Xinyuan-LilyGO/T-Embed-CC1101/hardware/SI446X/T-SI4463 V0.1-PIN.pdf

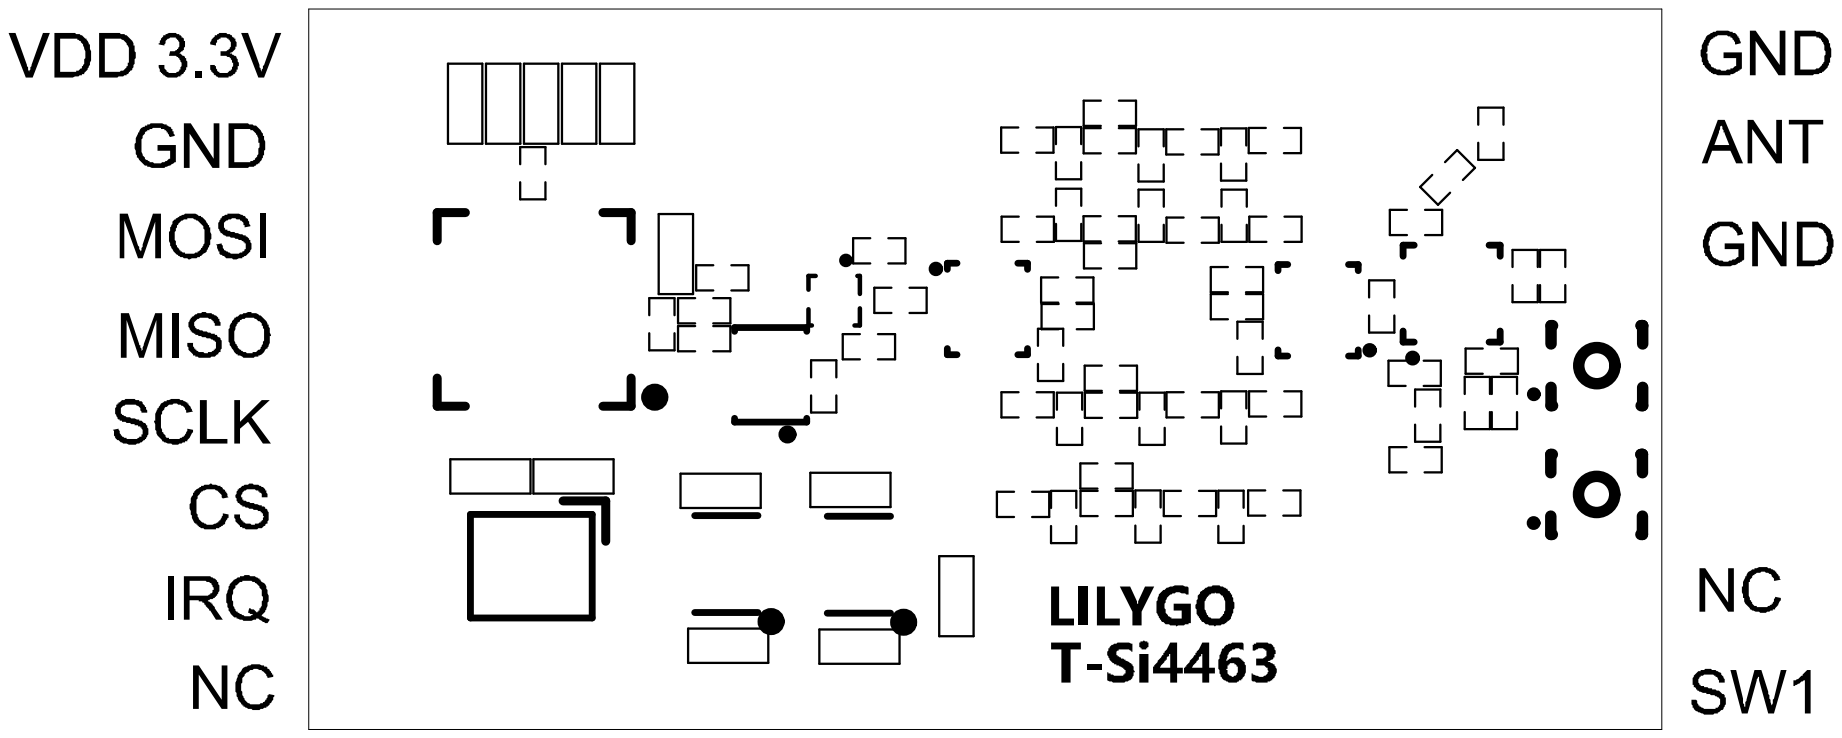
[picture p25: page 1]
