Xinyuan-LilyGO/T-Embed-CC1101/examples/factory_test/factory_test.ino

#include "utilities.h"
#define XPOWERS_CHIP_BQ25896
#include <XPowersLib.h>
#include "ui.h"
#include "TFT_eSPI.h"
#include "Audio.h"
#include <IRremoteESP8266.h>
#include <IRsend.h>
#include <IRrecv.h>
#include <IRutils.h>

const uint16_t kIrLed = 2;  // ESP8266 GPIO pin to use. Recommended: 4 (D2).
const uint16_t kRecvPin = 1;
IRsend irsend(kIrLed);  // Set the GPIO to be used to sending the message.
IRrecv irrecv(kRecvPin);
decode_results results;

uint64_t IR_recv_value = 0x10000000UL;
char IR_recv_protocol[20] = "WAIT";
uint16_t IR_recv_bits = 0;
bool IR_recv_repeat = false;
uint32_t IR_recv_count = 0;
uint32_t IR_recv_last_ms = 0;

/*********************************************************************************
 *                               DEFINE
 *********************************************************************************/
#define FORMAT_SPIFFS_IF_FAILED true

#define NFC_PRIORITY     (configMAX_PRIORITIES - 1)
#define LORA_PRIORITY    (configMAX_PRIORITIES - 2)
#define WS2812_PRIORITY  (configMAX_PRIORITIES - 3)
#define BATTERY_PRIORITY (configMAX_PRIORITIES - 4)
#define NRF24_PRIORITY   (tskIDLE_PRIORITY + 2)

/*********************************************************************************
 *                              EXTERN
 *********************************************************************************/
extern uint8_t display_rotation;
extern uint8_t setting_theme;
/*********************************************************************************
 *                              TYPEDEFS
 *********************************************************************************/

Audio audio(false, 3, I2S_NUM_1);
XPowersPPM PPM;
BQ27220 bq27220;
uint32_t cycleInterval;
SemaphoreHandle_t radioLock;

TaskHandle_t nfc_handle;
TaskHandle_t lora_handle;
TaskHandle_t ws2812_handle;
TaskHandle_t battery_handle;
TaskHandle_t nrf24_handle;

// wifi
// char wifi_ssid[WIFI_SSID_MAX_LEN] = "xinyuandianzi";
// char wifi_password[WIFI_PSWD_MAX_LEN] = "AA15994823428";
char wifi_ssid[WIFI_SSID_MAX_LEN] = {0};
char wifi_password[WIFI_PSWD_MAX_LEN] = {0};
const char *ntpServer1 = "pool.ntp.org";
const char* ntpServer2 = "time.nist.gov";
bool wifi_is_connect = false;
bool wifi_eeprom_upd = false;
static struct tm timeinfo;
static uint32_t last_tick;

static constexpr uint16_t PPM_INPUT_LIMIT_MA = 1000;
static constexpr uint16_t PPM_CHARGE_TARGET_MV = 4208;
static constexpr uint16_t PPM_PRECHARGE_MA = 128;
static constexpr uint16_t PPM_TERMINATION_MA = 128;
static constexpr uint16_t PPM_FAST_CHARGE_MA = 512;
static constexpr uint16_t PPM_SYS_POWERDOWN_MV = 3300;
static constexpr uint32_t PPM_RECOVERY_RETRY_INTERVAL_MS = 1500;
static constexpr int16_t PPM_RECOVERY_DISCHARGE_CURRENT_MA = -50;
static constexpr uint32_t MIC_SAMPLE_PERIOD_MS = 5;
static constexpr TickType_t MIC_SAMPLE_TIMEOUT_TICKS = 0;
static constexpr uint32_t BOARD_USER_KEY_DEBOUNCE_MS = 30;

static bool ppm_recovery_enabled = true;
static bool ppm_recovery_usb_was_present = false;
static uint32_t ppm_recovery_last_ms = 0;

// eeprom
uint8_t eeprom_ssid[WIFI_SSID_MAX_LEN];
uint8_t eeprom_pswd[WIFI_PSWD_MAX_LEN];

// mic
int16_t i2s_readraw_buff[SAMPLE_SIZE] = {0};
size_t bytes_read = 0;
int i2s_mic_cnt = 0;

/*********************************************************************************
 *                              FUNCTION
 *********************************************************************************/

static void board_spi_init_cs_pin(uint8_t pin)
{
    pinMode(pin, OUTPUT);
    digitalWrite(pin, HIGH);
}

void board_spi_deselect_all(void)
{
    digitalWrite(DISPLAY_CS, HIGH);
    digitalWrite(BOARD_SD_CS, HIGH);
    digitalWrite(BOARD_LORA_CS, HIGH);
    digitalWrite(BOARD_NRF24_CS, HIGH);
}

void board_spi_prepare_display(void)
{
    board_spi_deselect_all();
}

void board_spi_prepare_lora(void)
{
    board_spi_deselect_all();
}

void board_spi_prepare_nrf24(void)
{
    board_spi_deselect_all();
}

void board_spi_prepare_sd(void)
{
    board_spi_deselect_all();
}

void board_spi_init_shared_bus(void)
{
    board_spi_init_cs_pin(DISPLAY_CS);
    board_spi_init_cs_pin(BOARD_SD_CS);
    board_spi_init_cs_pin(BOARD_LORA_CS);
    board_spi_init_cs_pin(BOARD_NRF24_CS);

    pinMode(BOARD_NRF24_CE, OUTPUT);
    digitalWrite(BOARD_NRF24_CE, LOW);

    board_spi_deselect_all();
    SPI.begin(BOARD_SPI_SCK, BOARD_SPI_MISO, BOARD_SPI_MOSI);
}

void eeprom_default_val(void)
{
    char wifi_ssid[WIFI_SSID_MAX_LEN] = "xinyuandianzi";
    char wifi_password[WIFI_PSWD_MAX_LEN] = "AA15994823428";

    EEPROM.write(0, EEPROM_UPDATA_FLAG_NUM);
    for(int i = WIFI_SSID_EEPROM_ADDR; i < WIFI_SSID_EEPROM_ADDR + WIFI_SSID_MAX_LEN; i++) {
        int k = i - WIFI_SSID_EEPROM_ADDR;
        if(k < WIFI_SSID_MAX_LEN) {
            EEPROM.write(i, wifi_ssid[k]);
        } else {
            EEPROM.write(i, 0x00);
        }
    }
    for(int i = WIFI_PSWD_EEPROM_ADDR; i < WIFI_PSWD_EEPROM_ADDR + WIFI_PSWD_MAX_LEN; i++) {
        int k = i - WIFI_PSWD_EEPROM_ADDR;
        if(k < WIFI_PSWD_MAX_LEN) {
            EEPROM.write(i, wifi_password[k]);
        } else {
            EEPROM.write(i, 0x00);
        }
    }
    EEPROM.commit();
    wifi_eeprom_upd = true;
}

void eeprom_wr(int addr, uint8_t val)
{
    if(wifi_eeprom_upd == false) {
        eeprom_default_val();
    }
    EEPROM.write(addr, val);
    EEPROM.commit();
    Serial.printf("eeprom_wr %d:%d\n", addr, val);
}

void eeprom_wr_wifi(const char *ssid, uint16_t ssid_len, const char *pwsd, uint16_t pwsd_len)
{
    Serial.printf("eeprom_wr_wifi \n%s:%d\n%s:%d\n", ssid, ssid_len, pwsd, pwsd_len);
    if(ssid_len > WIFI_SSID_MAX_LEN) 
        ssid_len = WIFI_SSID_MAX_LEN;
    if(pwsd_len > WIFI_PSWD_MAX_LEN)
        pwsd_len = WIFI_PSWD_MAX_LEN;

    if(wifi_eeprom_upd == false) {
        EEPROM.write(0, EEPROM_UPDATA_FLAG_NUM);
        wifi_eeprom_upd = true;
    }

    for(int i = WIFI_SSID_EEPROM_ADDR; i < WIFI_SSID_EEPROM_ADDR + WIFI_SSID_MAX_LEN; i++) {
        int k = i - WIFI_SSID_EEPROM_ADDR;
        if(k < ssid_len) {
            EEPROM.write(i, ssid[k]);
        } else {
            EEPROM.write(i, 0x00);
        }
    }
    for(int i = WIFI_PSWD_EEPROM_ADDR; i < WIFI_PSWD_EEPROM_ADDR + WIFI_PSWD_MAX_LEN; i++) {
        int k = i - WIFI_PSWD_EEPROM_ADDR;
        if(k < pwsd_len) {
            EEPROM.write(i, pwsd[k]);
        } else {
            EEPROM.write(i, 0x00);
        }
    }
    EEPROM.commit();
}

void eeprom_init()
{
    if (!EEPROM.begin(EEPROM_SIZE_MAX)) {
        Serial.println("failed to initialise EEPROM"); delay(1000000);
    }
    uint8_t frist_flag = EEPROM.read(0);
    if(frist_flag == EEPROM_UPDATA_FLAG_NUM) {
        for(int i = WIFI_SSID_EEPROM_ADDR; i < WIFI_SSID_EEPROM_ADDR + WIFI_SSID_MAX_LEN; i++) {
            wifi_ssid[i - WIFI_SSID_EEPROM_ADDR] = EEPROM.read(i);
        }
        for(int i = WIFI_PSWD_EEPROM_ADDR; i < WIFI_PSWD_EEPROM_ADDR + WIFI_PSWD_MAX_LEN; i++) {
            wifi_password[i - WIFI_PSWD_EEPROM_ADDR] = EEPROM.read(i);
        }

        wifi_eeprom_upd = true;
        

        uint8_t theme = EEPROM.read(UI_THEME_EEPROM_ADDR);
        uint8_t rotation = EEPROM.read(UI_ROTATION_EEPROM_ADDR);

        setting_theme = (theme == 255 ? 0 : theme);
        display_rotation = (rotation == 1 ? 1 : 3);

        Serial.println("*************** eeprom ****************");
        Serial.printf("eeprom flag: %d\n", frist_flag);
        Serial.printf("eeprom SSID: %s\n", wifi_ssid);
        Serial.printf("eeprom PWSD: %s\n", wifi_password);
        Serial.printf("eeprom theme: %d\n", theme);
        Serial.printf("eeprom rotation: %d\n", rotation);
        Serial.println("***************************************");
    }
}

void multi_thread_create(void)
{
    xTaskCreate(nfc_task, "nfc_task", 1024 * 3, NULL, NFC_PRIORITY, &nfc_handle);
    xTaskCreate(lora_task, "lora_task", 1024 * 2, NULL, LORA_PRIORITY, &lora_handle);
    xTaskCreate(ws2812_task, "ws2812_task", 1024 * 2, NULL, WS2812_PRIORITY, &ws2812_handle);
    xTaskCreate(nrf24_task, "nrf24_task", 1024 * 10, NULL, NRF24_PRIORITY, &nrf24_handle);
}

void wifi_init(void)
{
    Serial.printf("SSID len: %d\n", strlen(wifi_ssid));
    Serial.printf("PWSD len: %d\n", strlen(wifi_password));
    if(strlen(wifi_ssid) == 0 || strlen(wifi_password) == 0) {
        return;
    }

    WiFi.begin(wifi_ssid, wifi_password);
    wl_status_t wifi_state = WiFi.status();
    last_tick = millis();
    while (wifi_state != WL_CONNECTED){
        delay(500);
        Serial.print(".");
        wifi_state = WiFi.status();
        if(wifi_state == WL_CONNECTED){
            wifi_is_connect = true;
            Serial.println("WiFi connected!");
            configTime(8 * 3600, 0, ntpServer1, ntpServer2);
            break;
        }
        if (millis() - last_tick > 5000) {
            Serial.println("WiFi connected falied!");
            last_tick = millis();
            break;
        }
    }
}

static void msg_send_event(lv_timer_t *t)
{
    if(wifi_is_connect == true){
        if (!getLocalTime(&timeinfo)){
            Serial.println("Failed to obtain time");
            return;
        }
        // Serial.println(&timeinfo, "%F %T %A"); // 格式化输出
        timeinfo.tm_hour = timeinfo.tm_hour % 12;
        lv_msg_send(MSG_CLOCK_HOUR, &timeinfo.tm_hour);
        lv_msg_send(MSG_CLOCK_MINUTE, &timeinfo.tm_min);
        lv_msg_send(MSG_CLOCK_SECOND, &timeinfo.tm_sec);
    }
}

static void msg_subsribe_event(void * s, lv_msg_t * msg)
{
    LV_UNUSED(s);

    switch (msg->id)
    {
        case MSG_UI_ROTATION_ST:{ 
            
        }break;
        case MSG_UI_THEME_MODE:{
            
        }break;
    
        default:
            break;
    }
}

void listDir(fs::FS &fs, const char * dirname, uint8_t levels){
    Serial.printf("Listing spiffs directory: %s\n", dirname);

    File root = fs.open(dirname);
    if(!root){
        Serial.println("- failed to open directory");
        return;
    }
    if(!root.isDirectory()){
        Serial.println(" - not a directory");
        return;
    }

    File file = root.openNextFile();
    while(file){
        if(file.isDirectory()){
            Serial.print("  DIR : ");
            Serial.println(file.name());
            if(levels){
                listDir(fs, file.path(), levels -1);
            }
        } else {
            Serial.print("  FILE: ");
            Serial.print(file.name());
            Serial.print("\tSIZE: ");
            Serial.println(file.size());
        }
        file = root.openNextFile();
    }
}

extern int music_idx;
extern char *music_list[20];

void scr8_read_music_from_SD(void)
{
    board_spi_prepare_sd();

    File root = SD.open("/music");
    if(!root){
        Serial.println("Failed to open directory");
        return;
    }

    int i = 0;
    File file = root.openNextFile();
    while(file) {
        if(!file.isDirectory()) {
            
            char *file_name = (char *)file.name();
            uint16_t file_name_len = strlen(file_name);
            char *buf = (char *)ps_malloc(file_name_len + 1);
            strcpy(buf, file_name);
            music_list[i] = buf;
            i++;

            Serial.println(music_list[i-1]);
        }
        file = root.openNextFile();
    }
}

static bool ppm_usb_present(void)
{
    return PPM.isVbusIn() || (PPM.getVbusVoltage() >= 4000);
}

static void ppm_configure_charge_path(bool reset_registers)
{
    if (reset_registers) {
        PPM.resetDefault();
        delay(20);
    }

    PPM.disableWatchdog();
    PPM.exitHizMode();
    PPM.disableOTG();
    PPM.enableBatterPowerPath();
    PPM.disableCurrentLimitPin();
    PPM.enableAutomaticInputDetection();
    PPM.enableInputDetection();
    PPM.setInputCurrentLimit(PPM_INPUT_LIMIT_MA);
    PPM.setChargeTargetVoltage(PPM_CHARGE_TARGET_MV);
    PPM.setPrechargeCurr(PPM_PRECHARGE_MA);
    PPM.setTerminationCurr(PPM_TERMINATION_MA);
    PPM.setChargerConstantCurr(PPM_FAST_CHARGE_MA);
    PPM.enableMeasure();
    PPM.enableChargingTermination();
    PPM.setSysPowerDownVoltage(PPM_SYS_POWERDOWN_MV);
    PPM.enableCharge();
    PPM.getFaultStatus();
}

static bool ppm_needs_charge_recovery(void)
{
    if (!ppm_usb_present()) {
        return false;
    }

    uint16_t battery_mv = PPM.getBattVoltage();
    uint16_t target_mv = PPM.getChargeTargetVoltage();
    bool battery_needs_charge = (battery_mv == 0) || (target_mv == 0) || (battery_mv + 96 < target_mv);
    bool charge_path_invalid = PPM.isHizMode() || PPM.isEnableOTG() || !PPM.isEnableCharge();
    bool charge_state_missing = PPM.chargeStatus() == XPowersPPM::CHARGE_STATE_NO_CHARGE;
    bool power_not_good = !PPM.isPowerGood();
    bool battery_still_discharging = bq27220.getAverageCurrent() <= PPM_RECOVERY_DISCHARGE_CURRENT_MA;

    return charge_path_invalid || (battery_needs_charge && (charge_state_missing || power_not_good || battery_still_discharging));
}

static void ppm_service_charge_recovery(void)
{
    if (!ppm_recovery_enabled) {
        return;
    }

    bool usb_present = ppm_usb_present();
    if (usb_present && !ppm_recovery_usb_was_present) {
        Serial.println("VBUS inserted, restoring BQ25896 charge path.");
        ppm_configure_charge_path(true);
        ppm_recovery_last_ms = millis();
    } else if (usb_present && ppm_needs_charge_recovery()) {
        uint32_t now = millis();
        if ((ppm_recovery_last_ms == 0) || (now - ppm_recovery_last_ms >= PPM_RECOVERY_RETRY_INTERVAL_MS)) {
            Serial.printf("BQ25896 recovery: bus=%d chg=%d vbus=%umV vbat=%umV avg=%dmA hiz=%d otg=%d enchg=%d pg=%d\n",
                          (int)PPM.getBusStatus(),
                          (int)PPM.chargeStatus(),
                          PPM.getVbusVoltage(),
                          PPM.getBattVoltage(),
                          bq27220.getAverageCurrent(),
                          (int)PPM.isHizMode(),
                          (int)PPM.isEnableOTG(),
                          (int)PPM.isEnableCharge(),
                          (int)PPM.isPowerGood());
            ppm_configure_charge_path(true);
            ppm_recovery_last_ms = now;
        }
    }

    if (!usb_present) {
        ppm_recovery_last_ms = 0;
    }
    ppm_recovery_usb_was_present = usb_present;
}

void ppm_set_recovery_enabled(bool enabled)
{
    ppm_recovery_enabled = enabled;
    if (enabled) {
        ppm_recovery_usb_was_present = false;
        ppm_recovery_last_ms = 0;
    }
}

static bool board_user_key_pressed(void)
{
    static bool last_raw_state = HIGH;
    static bool stable_state = HIGH;
    static uint32_t last_change_ms = 0;

    bool raw_state = digitalRead(BOARD_USER_KEY);
    uint32_t now = millis();

    if (raw_state != last_raw_state) {
        last_raw_state = raw_state;
        last_change_ms = now;
    }

    if ((now - last_change_ms) >= BOARD_USER_KEY_DEBOUNCE_MS && stable_state != raw_state) {
        stable_state = raw_state;
        if (stable_state == LOW) {
            return true;
        }
    }

    return false;
}

void setup(void)
{
    bool pmu_ret = false;
    bool nfc_ret = false;
    bool lora_ret = false;

    // LCD, CC1101, SD and nRF24 share the same SPI lines, keep every device
    // deselected before any library touches the bus.
    board_spi_init_shared_bus();

    // Init system
    pinMode(DISPLAY_BL, OUTPUT);
    digitalWrite(DISPLAY_BL, LOW);

    pinMode(BOARD_PWR_EN, OUTPUT);
    digitalWrite(BOARD_PWR_EN, HIGH);  // Power on CC1101 and LED

    pinMode(BOARD_PN532_RF_REST, OUTPUT);
    digitalWrite(BOARD_PN532_RF_REST, HIGH); 

    pinMode(ENCODER_KEY, INPUT);
    pinMode(BOARD_USER_KEY, INPUT);

    pinMode(BOARD_PN532_IRQ, OPEN_DRAIN);

    Serial.begin(115200);
    Serial.print("setup() running core ID: ");
    Serial.println(xPortGetCoreID());

    irsend.begin();
    irrecv.enableIRIn(); 

    radioLock = xSemaphoreCreateBinary();
    assert(radioLock);
    xSemaphoreGive(radioLock);

    init_microphone();

    // iic scan
    byte error, address;
    int nDevices = 0;
    Serial.println("Scanning for I2C devices ...");
    Wire.begin(BOARD_I2C_SDA, BOARD_I2C_SCL);
    for(address = 0x01; address < 0x7F; address++){
        Wire.beginTransmission(address);
        // 0: success.
        // 1: data too long to fit in transmit buffer.
        // 2: received NACK on transmit of address.
        // 3: received NACK on transmit of data.
        // 4: other error.
        // 5: timeout
        error = Wire.endTransmission();
        if(error == 0){ // 0: success.
            nDevices++;
            if(address == BOARD_I2C_ADDR_1) {
                nfc_ret = true;
                log_i("I2C device found PN532 at address 0x%x\n", address);
            } else if(address == BOARD_I2C_ADDR_2) {
                pmu_ret = true;
                log_i("I2C device found at BQ27220 address 0x%x\n", address);
            } else if(address == BOARD_I2C_ADDR_3) {
                lora_ret = true;
                log_i("I2C device found at BQ25896 address 0x%x\n", address);
            }
        }
    }
    if (nDevices == 0){
        Serial.println("No I2C devices found");
    }

    if(!SPIFFS.begin(FORMAT_SPIFFS_IF_FAILED)){
        Serial.println("SPIFFS Mount Failed");
        return;
    }

    Serial.println("*************** SPIFFS ****************");
    listDir(SPIFFS, "/", 0);
    Serial.println("**************************************");

    eeprom_init();

    // wifi_init();
    configTime(8 * 3600, 0, ntpServer1, ntpServer2);

    pmu_ret = PPM.init(Wire, BOARD_I2C_SDA, BOARD_I2C_SCL, BQ25896_SLAVE_ADDRESS);
    if(pmu_ret) {
        ppm_configure_charge_path(true);

        Serial.printf("BQ25896 input limit: %d mA\n", PPM.getInputCurrentLimit());
        Serial.printf("BQ25896 fast charge current: %d mA\n", PPM.getChargerConstantCurr());
        Serial.printf("BQ25896 termination current: %d mA\n", PPM.getTerminationCurr());
        Serial.printf("BQ25896 sys power down voltage: %d mV\n", PPM.getSysPowerDownVoltage());
        // Turn off charging function
        // If USB is used as the only power input, it is best to turn off the charging function,
        // otherwise the VSYS power supply will have a sawtooth wave, affecting the discharge output capability.
        // PPM.disableCharge();


        // The OTG function needs to enable OTG, and set the OTG control pin to HIGH
        // After OTG is enabled, if an external power supply is plugged in, OTG will be turned off

        // PPM.enableOTG();
        // PPM.disableOTG();
        // pinMode(OTG_ENABLE_PIN, OUTPUT);
        // digitalWrite(OTG_ENABLE_PIN, HIGH);
    }

    bq27220.init();
   
    lora_init(); 

    if(nfc_ret)
        nfc_init();

    ws2812_init();

    // infared_init();

    nrf24_init();

    audio.setPinout(BOARD_VOICE_BCLK, BOARD_VOICE_LRCLK, BOARD_VOICE_DIN);
    audio.setVolume(21); // 0...21
    audio.connecttoFS(SPIFFS, "/001.mp3");

    // audio.connecttoFS(SD, "/music/My Anata.mp3");

    Serial.println("setup: ble_uart_init");
    ble_uart_init();
    delay(1);

    // init UI and display
    Serial.println("setup: ui_entry");
    ui_entry();
    delay(1);
    lv_timer_create(msg_send_event, 5000, NULL);
    // lvgl msg
    lv_msg_subsribe(MSG_UI_ROTATION_ST, msg_subsribe_event, NULL);
    lv_msg_subsribe(MSG_UI_THEME_MODE, msg_subsribe_event, NULL);

    // Force the first frame out before enabling the backlight so we don't
    // spend the SD probe window showing a lit-but-empty panel.
    Serial.println("setup: first lv_timer_handler");
    lv_timer_handler();
    digitalWrite(DISPLAY_BL, HIGH);
    delay(1);

    Serial.println("setup: sd_init");
    sd_init();
    Serial.println("setup: scr8_read_music_from_SD");
    scr8_read_music_from_SD();
    delay(1);

    Serial.println("setup: multi_thread_create");
    multi_thread_create();

    // for(int i = 0; i < WS2812_NUM_LEDS*10; i++) {
    //     ws2812_pos_demo(i);
    //     delay(15);
    // }
    // ws2812_set_color(CRGB::Black);

    
}

int file_cnt = 0;
extern bool music_is_running;

void loop(void)
{
    static uint32_t last_mic_sample_ms = 0;

    audio.loop();

    lv_timer_handler();
    ble_uart_service();

    ppm_service_charge_recovery();

    if (board_user_key_pressed()) {
        Serial.println("BOARD_USER_KEY pressed");
        prompt_info("BOARD_USER_KEY pressed", 800);
    }

    if(music_is_running == false) {
        if (irrecv.decode(&results)) {
            // print() & println() can't handle printing long longs. (uint64_t)
            serialPrintUint64(results.value, HEX);
            IR_recv_value = results.value;
            IR_recv_bits = results.bits;
            IR_recv_repeat = results.repeat;
            IR_recv_count++;
            IR_recv_last_ms = millis();

            String protocol = typeToString(results.decode_type, results.repeat);
            protocol.toUpperCase();
            strncpy(IR_recv_protocol, protocol.c_str(), sizeof(IR_recv_protocol) - 1);
            IR_recv_protocol[sizeof(IR_recv_protocol) - 1] = '\0';
            Serial.println("");
            irrecv.resume();  // Receive the next value
        }

        uint32_t now = millis();
        if ((now - last_mic_sample_ms) >= MIC_SAMPLE_PERIOD_MS) {
            last_mic_sample_ms = now;
            if (i2s_read((i2s_port_t)EXAMPLE_I2S_CH,
                         (char *)i2s_readraw_buff,
                         sizeof(i2s_readraw_buff),
                         &bytes_read,
                         MIC_SAMPLE_TIMEOUT_TICKS) == ESP_OK) {
                size_t sample_count = bytes_read / sizeof(i2s_readraw_buff[0]);
                if (sample_count > SAMPLE_SIZE) {
                    sample_count = SAMPLE_SIZE;
                }

                for(size_t i = 0; i < sample_count; i++) {
                    if(i2s_readraw_buff[i] > 0) {
                        i2s_mic_cnt++;
                    }
                }
            }
        }
    }

    delay(1);
}
