Xinyuan-LilyGO/T-Embed-CC1101/script/gen_esp32part.py

#!/usr/bin/env python
#
# ESP32 partition table generation tool
#
# Converts partition tables to/from CSV and binary formats.
#
# See https://docs.espressif.com/projects/esp-idf/en/latest/api-guides/partition-tables.html
# for explanation of partition table structure and uses.
#
# SPDX-FileCopyrightText: 2016-2021 Espressif Systems (Shanghai) CO LTD
# SPDX-License-Identifier: Apache-2.0

from __future__ import division, print_function, unicode_literals

import argparse
import binascii
import errno
import hashlib
import os
import re
import struct
import sys

MAX_PARTITION_LENGTH = 0xC00   # 3K for partition data (96 entries) leaves 1K in a 4K sector for signature
MD5_PARTITION_BEGIN = b'\xEB\xEB' + b'\xFF' * 14  # The first 2 bytes are like magic numbers for MD5 sum
PARTITION_TABLE_SIZE  = 0x1000  # Size of partition table

MIN_PARTITION_SUBTYPE_APP_OTA = 0x10
NUM_PARTITION_SUBTYPE_APP_OTA = 16

__version__ = '1.2'

APP_TYPE = 0x00
DATA_TYPE = 0x01

TYPES = {
    'app': APP_TYPE,
    'data': DATA_TYPE,
}


def get_ptype_as_int(ptype):
    """ Convert a string which might be numeric or the name of a partition type to an integer """
    try:
        return TYPES[ptype]
    except KeyError:
        try:
            return int(ptype, 0)
        except TypeError:
            return ptype


# Keep this map in sync with esp_partition_subtype_t enum in esp_partition.h
SUBTYPES = {
    APP_TYPE: {
        'factory': 0x00,
        'test': 0x20,
    },
    DATA_TYPE: {
        'ota': 0x00,
        'phy': 0x01,
        'nvs': 0x02,
        'coredump': 0x03,
        'nvs_keys': 0x04,
        'efuse': 0x05,
        'undefined': 0x06,
        'esphttpd': 0x80,
        'fat': 0x81,
        'spiffs': 0x82,
    },
}


def get_subtype_as_int(ptype, subtype):
    """ Convert a string which might be numeric or the name of a partition subtype to an integer """
    try:
        return SUBTYPES[get_ptype_as_int(ptype)][subtype]
    except KeyError:
        try:
            return int(subtype, 0)
        except TypeError:
            return subtype


ALIGNMENT = {
    APP_TYPE: 0x10000,
    DATA_TYPE: 0x4,
}


STRICT_DATA_ALIGNMENT = 0x1000


def get_alignment_for_type(ptype):
    return ALIGNMENT.get(ptype, ALIGNMENT[DATA_TYPE])


quiet = False
md5sum = True
secure = False
offset_part_table = 0


def status(msg):
    """ Print status message to stderr """
    if not quiet:
        critical(msg)


def critical(msg):
    """ Print critical message to stderr """
    sys.stderr.write(msg)
    sys.stderr.write('\n')
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
